swharden/PressureSensor/builds/2.0/software/SerialManager.cpp

/* 
* SerialManager.cpp
*
* Created: 9/20/2023 8:44:44 PM
* Author: scott
*/


#include "SerialManager.h"

// default constructor
SerialManager::SerialManager()
{
} //SerialManager

// default destructor
SerialManager::~SerialManager()
{
} //~SerialManager
